plymouth-roco/Team-gama-hand/Images/94977785_176457680199136_9087925780704395264_n.jpg

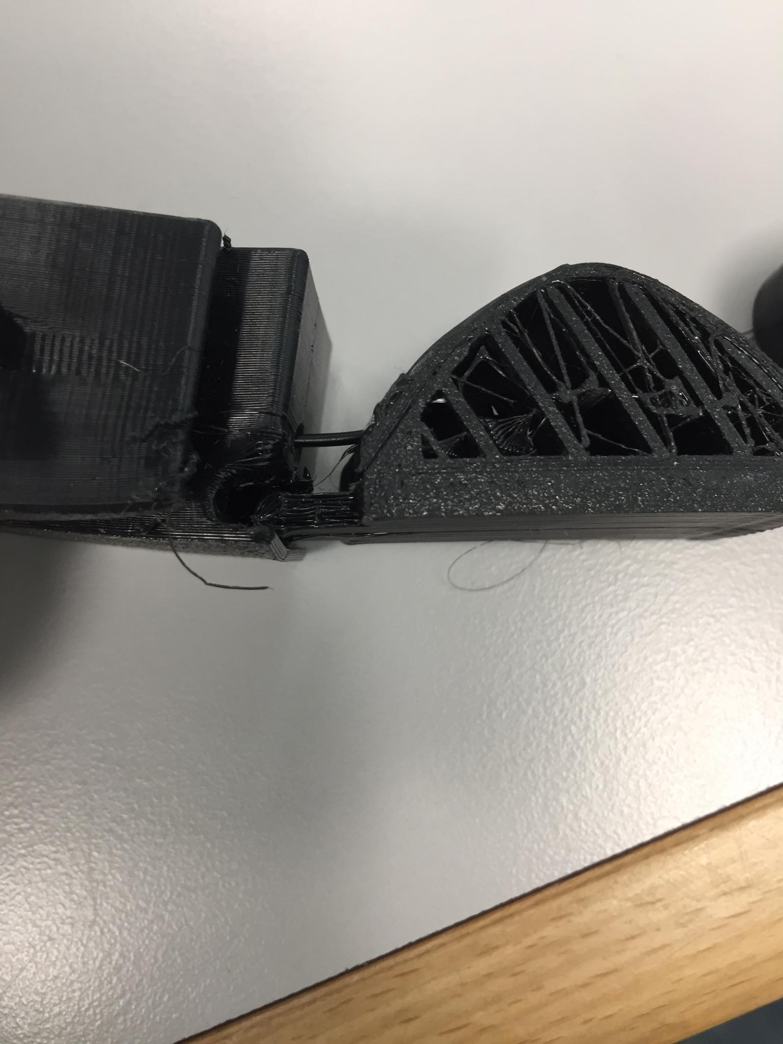
Images/94977785_176457680199136_9087925780704395264_n.jpg
