plymouth-roco/Team-gama-hand/Images/95097815_244433036776110_3921395004848734208_n (1).jpg

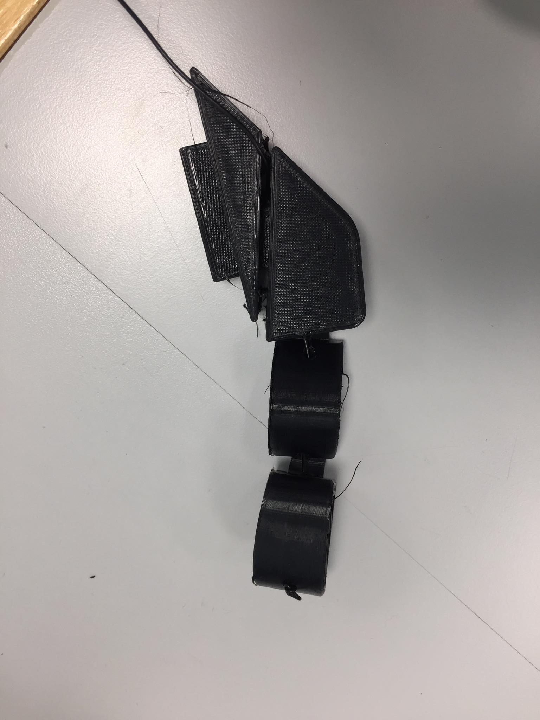
Images/95097815_244433036776110_3921395004848734208_n (1).jpg
